Alban098/Breadboard-CPU-Emulator/schematics/ALU.kicad_sch

## KiCad design schematics/ALU.kicad_sch (2024-06-02)

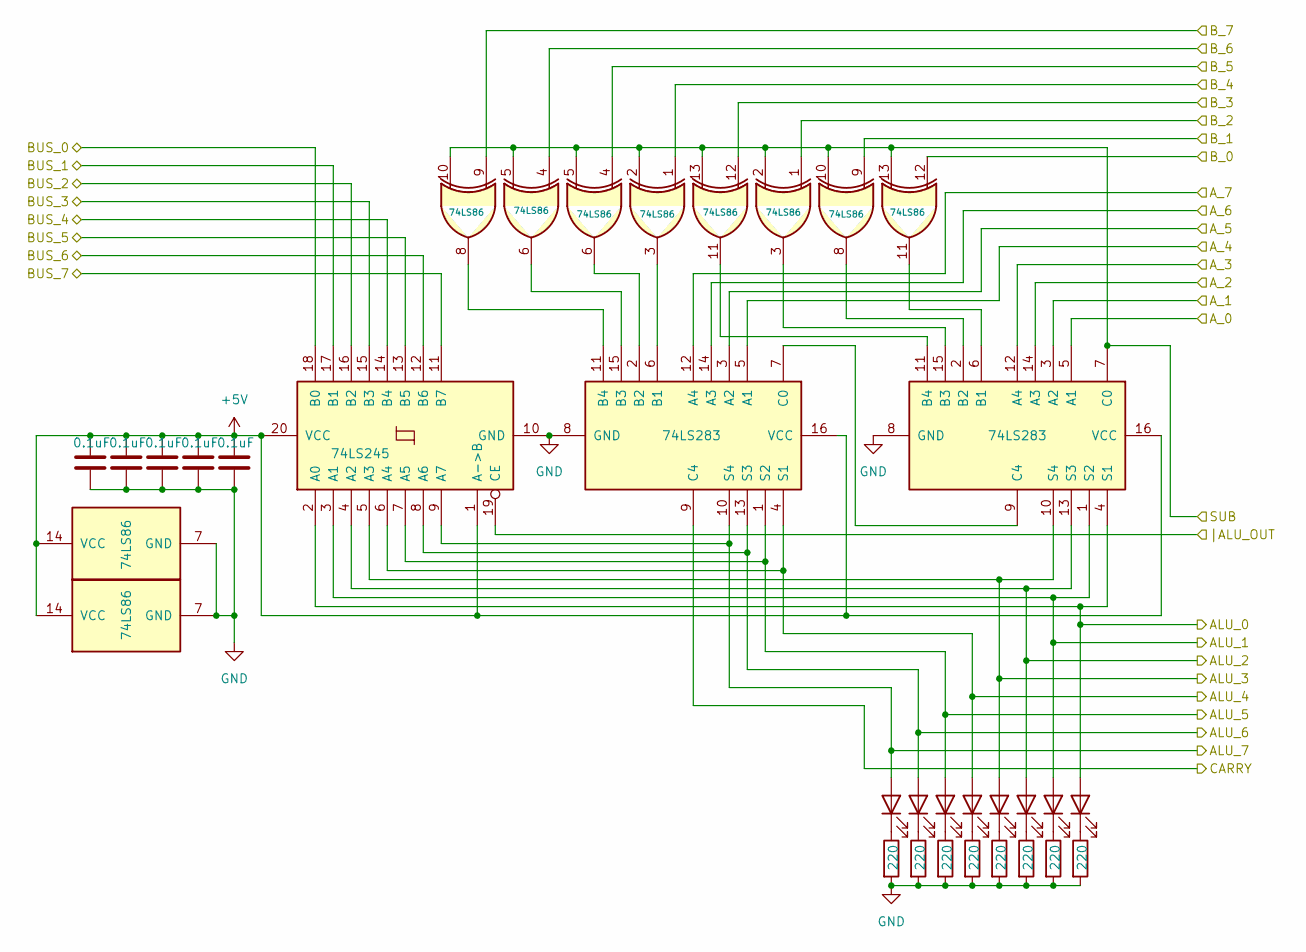
[picture p14: schematic ALU.kicad_sch]

Parts:
C1, C2, C3, C4, C5: 0.1uF
D1, D2, D3, D4, D5, D6, D7, D8: LED
R1, R2, R3, R4, R5, R6, R7, R8: 220
U1, U2: 74LS283
U3: 74LS245
U4, U5: 74LS86

Connections:
+5V: C1.1, C2.1, C3.1, C4.1, C5.1, U1.16 (VCC), U2.16 (VCC), U3.1 (A->B), U3.20 (VCC), U4.14 (VCC), U5.14 (VCC)
ALU_0: D8.2 (A), U2.4 (S1), U3.2 (A0)
ALU_1: D7.2 (A), U2.1 (S2), U3.3 (A1)
ALU_2: D6.2 (A), U2.13 (S3), U3.4 (A2)
ALU_3: D5.2 (A), U2.10 (S4), U3.5 (A3)
ALU_4: D4.2 (A), U1.4 (S1), U3.6 (A4)
ALU_5: D3.2 (A), U1.1 (S2), U3.7 (A5)
ALU_6: D2.2 (A), U1.13 (S3), U3.8 (A6)
ALU_7: D1.2 (A), U1.10 (S4), U3.9 (A7)
A_0: U2.5 (A1)
A_1: U2.3 (A2)
A_2: U2.14 (A3)
A_3: U2.12 (A4)
A_4: U1.5 (A1)
A_5: U1.3 (A2)
A_6: U1.14 (A3)
A_7: U1.12 (A4)
BUS_0: U3.18 (B0)
BUS_1: U3.17 (B1)
BUS_2: U3.16 (B2)
BUS_3: U3.15 (B3)
BUS_4: U3.14 (B4)
BUS_5: U3.13 (B5)
BUS_6: U3.12 (B6)
BUS_7: U3.11 (B7)
B_0: U5.12
B_1: U5.9
B_2: U5.1
B_3: U4.12
B_4: U4.1
B_5: U5.4
B_6: U4.4
B_7: U4.9
CARRY: U1.9 (C4)
GND: C1.2, C2.2, C3.2, C4.2, C5.2, R1.2, R2.2, R3.2, R4.2, R5.2, R6.2, R7.2, R8.2, U1.8 (GND), U2.8 (GND), U3.10 (GND), U4.7 (GND), U5.7 (GND)
unnamed: D1.1 (K), R1.1
unnamed: D2.1 (K), R2.1
unnamed: D3.1 (K), R3.1
unnamed: D4.1 (K), R4.1
unnamed: D5.1 (K), R5.1
unnamed: D6.1 (K), R6.1
unnamed: D7.1 (K), R7.1
unnamed: D8.1 (K), R8.1
unnamed: U1.2 (B2), U5.6
unnamed: U1.6 (B1), U4.3
unnamed: U1.7 (C0), U2.9 (C4)
unnamed: U1.11 (B4), U4.8
unnamed: U1.15 (B3), U4.6
unnamed: U2.2 (B2), U5.8
unnamed: U2.6 (B1), U5.11
unnamed: U2.11 (B4), U4.11
unnamed: U2.15 (B3), U5.3
SUB: U2.7 (C0), U4.2, U4.5, U4.10, U4.13, U5.2, U5.5, U5.10, U5.13
|ALU_OUT: U3.19 (CE)
