Alban098/Breadboard-CPU-Emulator/schematics/A_Register.kicad_sch

## KiCad design schematics/A_Register.kicad_sch (2024-06-02)

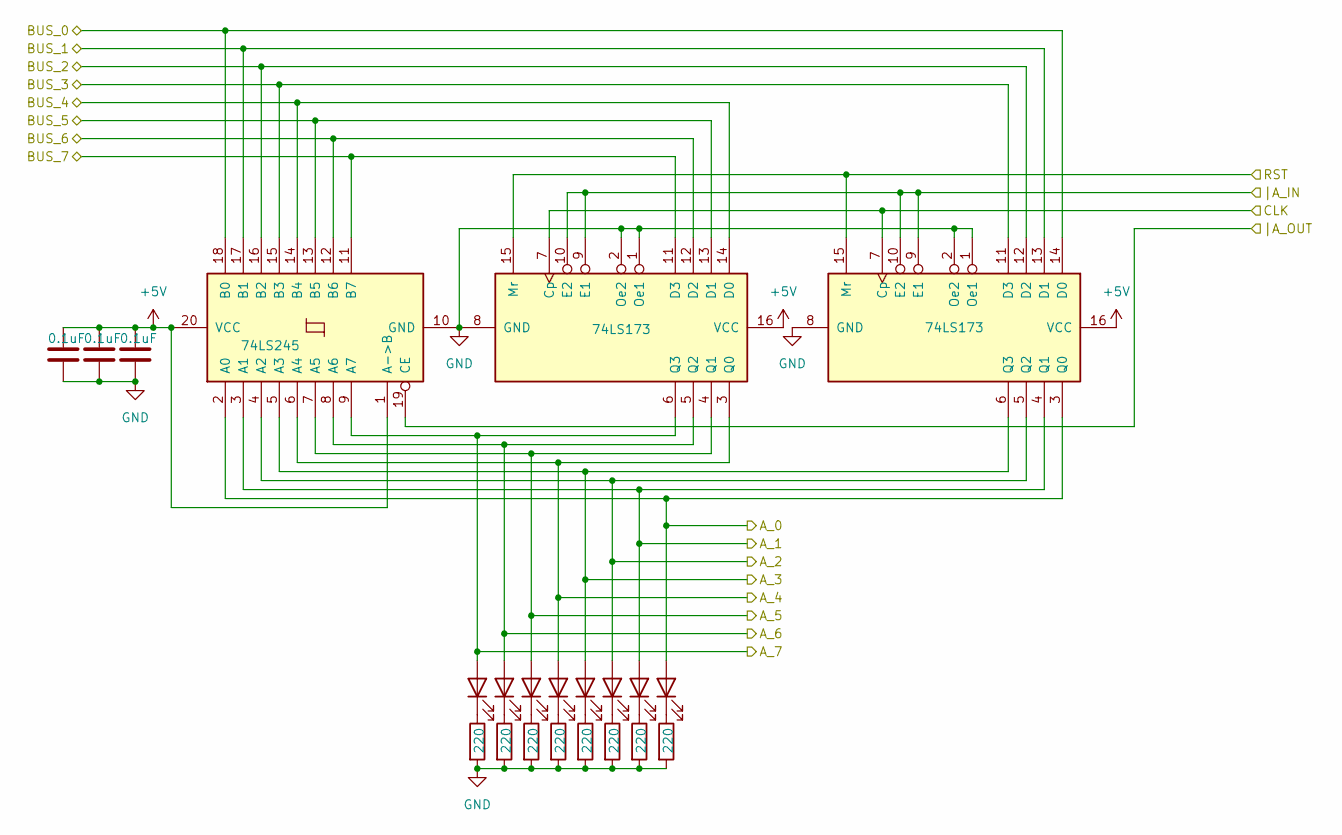
[picture p15: schematic A_Register.kicad_sch]

Parts:
C1, C2, C3: 0.1uF
D1, D2, D3, D4, D5, D6, D7, D8: LED
R1, R2, R3, R4, R5, R6, R7, R8: 220
U1, U2: 74LS173
U3: 74LS245

Connections:
+5V: C1.1, C2.1, C3.1, U1.16 (VCC), U2.16 (VCC), U3.1 (A->B), U3.20 (VCC)
A_0: D8.2 (A), U2.3 (Q0), U3.2 (A0)
A_1: D7.2 (A), U2.4 (Q1), U3.3 (A1)
A_2: D6.2 (A), U2.5 (Q2), U3.4 (A2)
A_3: D5.2 (A), U2.6 (Q3), U3.5 (A3)
A_4: D4.2 (A), U1.3 (Q0), U3.6 (A4)
A_5: D3.2 (A), U1.4 (Q1), U3.7 (A5)
A_6: D2.2 (A), U1.5 (Q2), U3.8 (A6)
A_7: D1.2 (A), U1.6 (Q3), U3.9 (A7)
BUS_0: U2.14 (D0), U3.18 (B0)
BUS_1: U2.13 (D1), U3.17 (B1)
BUS_2: U2.12 (D2), U3.16 (B2)
BUS_3: U2.11 (D3), U3.15 (B3)
BUS_4: U1.14 (D0), U3.14 (B4)
BUS_5: U1.13 (D1), U3.13 (B5)
BUS_6: U1.12 (D2), U3.12 (B6)
BUS_7: U1.11 (D3), U3.11 (B7)
CLK: U1.7 (Cp), U2.7 (Cp)
GND: C1.2, C2.2, C3.2, R1.2, R2.2, R3.2, R4.2, R5.2, R6.2, R7.2, R8.2, U1.1 (Oe1), U1.2 (Oe2), U1.8 (GND), U2.1 (Oe1), U2.2 (Oe2), U2.8 (GND), U3.10 (GND)
unnamed: D1.1 (K), R1.1
unnamed: D2.1 (K), R2.1
unnamed: D3.1 (K), R3.1
unnamed: D4.1 (K), R4.1
unnamed: D5.1 (K), R5.1
unnamed: D6.1 (K), R6.1
unnamed: D7.1 (K), R7.1
unnamed: D8.1 (K), R8.1
RST: U1.15 (Mr), U2.15 (Mr)
|A_IN: U1.9 (E1), U1.10 (E2), U2.9 (E1), U2.10 (E2)
|A_OUT: U3.19 (CE)
