Alban098/Breadboard-CPU-Emulator/schematics/Clock_Module.kicad_sch

## KiCad design schematics/Clock_Module.kicad_sch (2024-12-01)

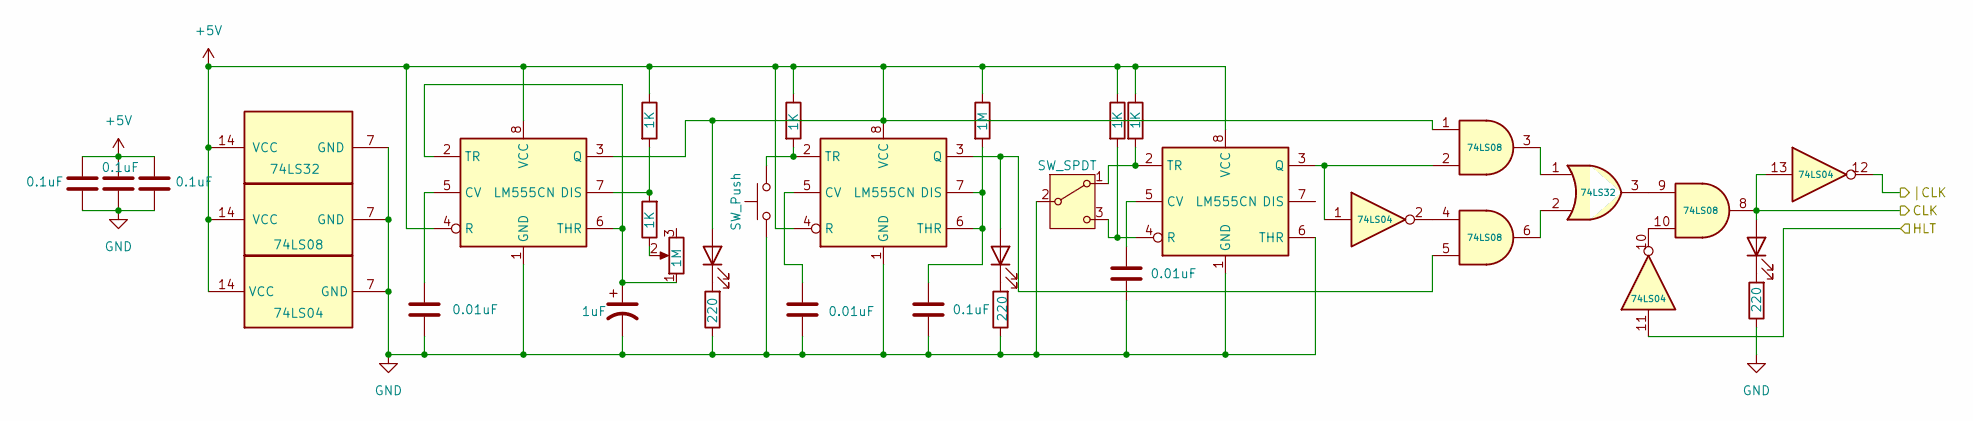
[picture p16: schematic Clock_Module.kicad_sch]

Parts:
1M: R_Potentiometer
C1, C3, C4: 0.01uF
C2, C5, C6, C8: 0.1uF
C7: 1uF
D1, D2, D3: LED
R1, R8, R9: 220
R2, R3, R4, R6, R7: 1K
R5: 1M
SW1: SW_SPDT
SW2: SW_Push
U1, U3, U7: LM555CN; DIP-8_W7.62mm
U4: 74LS08
U5: 74LS32
U6: 74LS04

Connections:
+5V: C5.2, C6.2, C8.2, D2.2 (A), R2.1, R3.1, R4.1, R5.1, R6.1, U1.3 (Q), U1.4 (R), U1.8 (VCC), U3.8 (VCC), U4.1, U4.14 (VCC), U5.14 (VCC), U6.14 (VCC), U7.4 (R), U7.8 (VCC)
CLK: D1.2 (A), U4.8, U6.13
GND: C1.2, C2.2, C3.2, C4.2, C5.1, C6.1, C7.2, C8.1, R1.1, R8.1, R9.1, SW1.2 (B), SW2.1, U1.1 (GND), U3.1 (GND), U3.6 (THR), U4.7 (GND), U5.7 (GND), U6.7 (GND), U7.1 (GND)
HLT: U6.11
unnamed: 1M.1, C7.1, U1.2 (TR), U1.6 (THR)
unnamed: 1M.2, R7.1
unnamed: C1.1, U3.5 (CV)
unnamed: C2.1, R5.2, U7.6 (THR), U7.7 (DIS)
unnamed: C3.1, U1.5 (CV)
unnamed: C4.1, U7.5 (CV)
unnamed: D1.1 (K), R1.2
unnamed: D2.1 (K), R8.2
unnamed: D3.1 (K), R9.2
unnamed: D3.2 (A), U4.5, U7.3 (Q)
unnamed: R2.2, SW1.1 (A), U3.2 (TR)
unnamed: R3.2, SW1.3 (C), U3.4 (R)
unnamed: R4.2, SW2.2, U7.2 (TR)
unnamed: R6.2, R7.2, U1.7 (DIS)
unnamed: U3.3 (Q), U4.2, U6.1
unnamed: U4.3, U5.1
unnamed: U4.4, U6.2
unnamed: U4.6, U5.2
unnamed: U4.9, U5.3
unnamed: U4.10, U6.10
|CLK: U6.12
