Alban098/Breadboard-CPU-Emulator/schematics/Control_Unit.kicad_sch

## KiCad design schematics/Control_Unit.kicad_sch (2025-01-03)

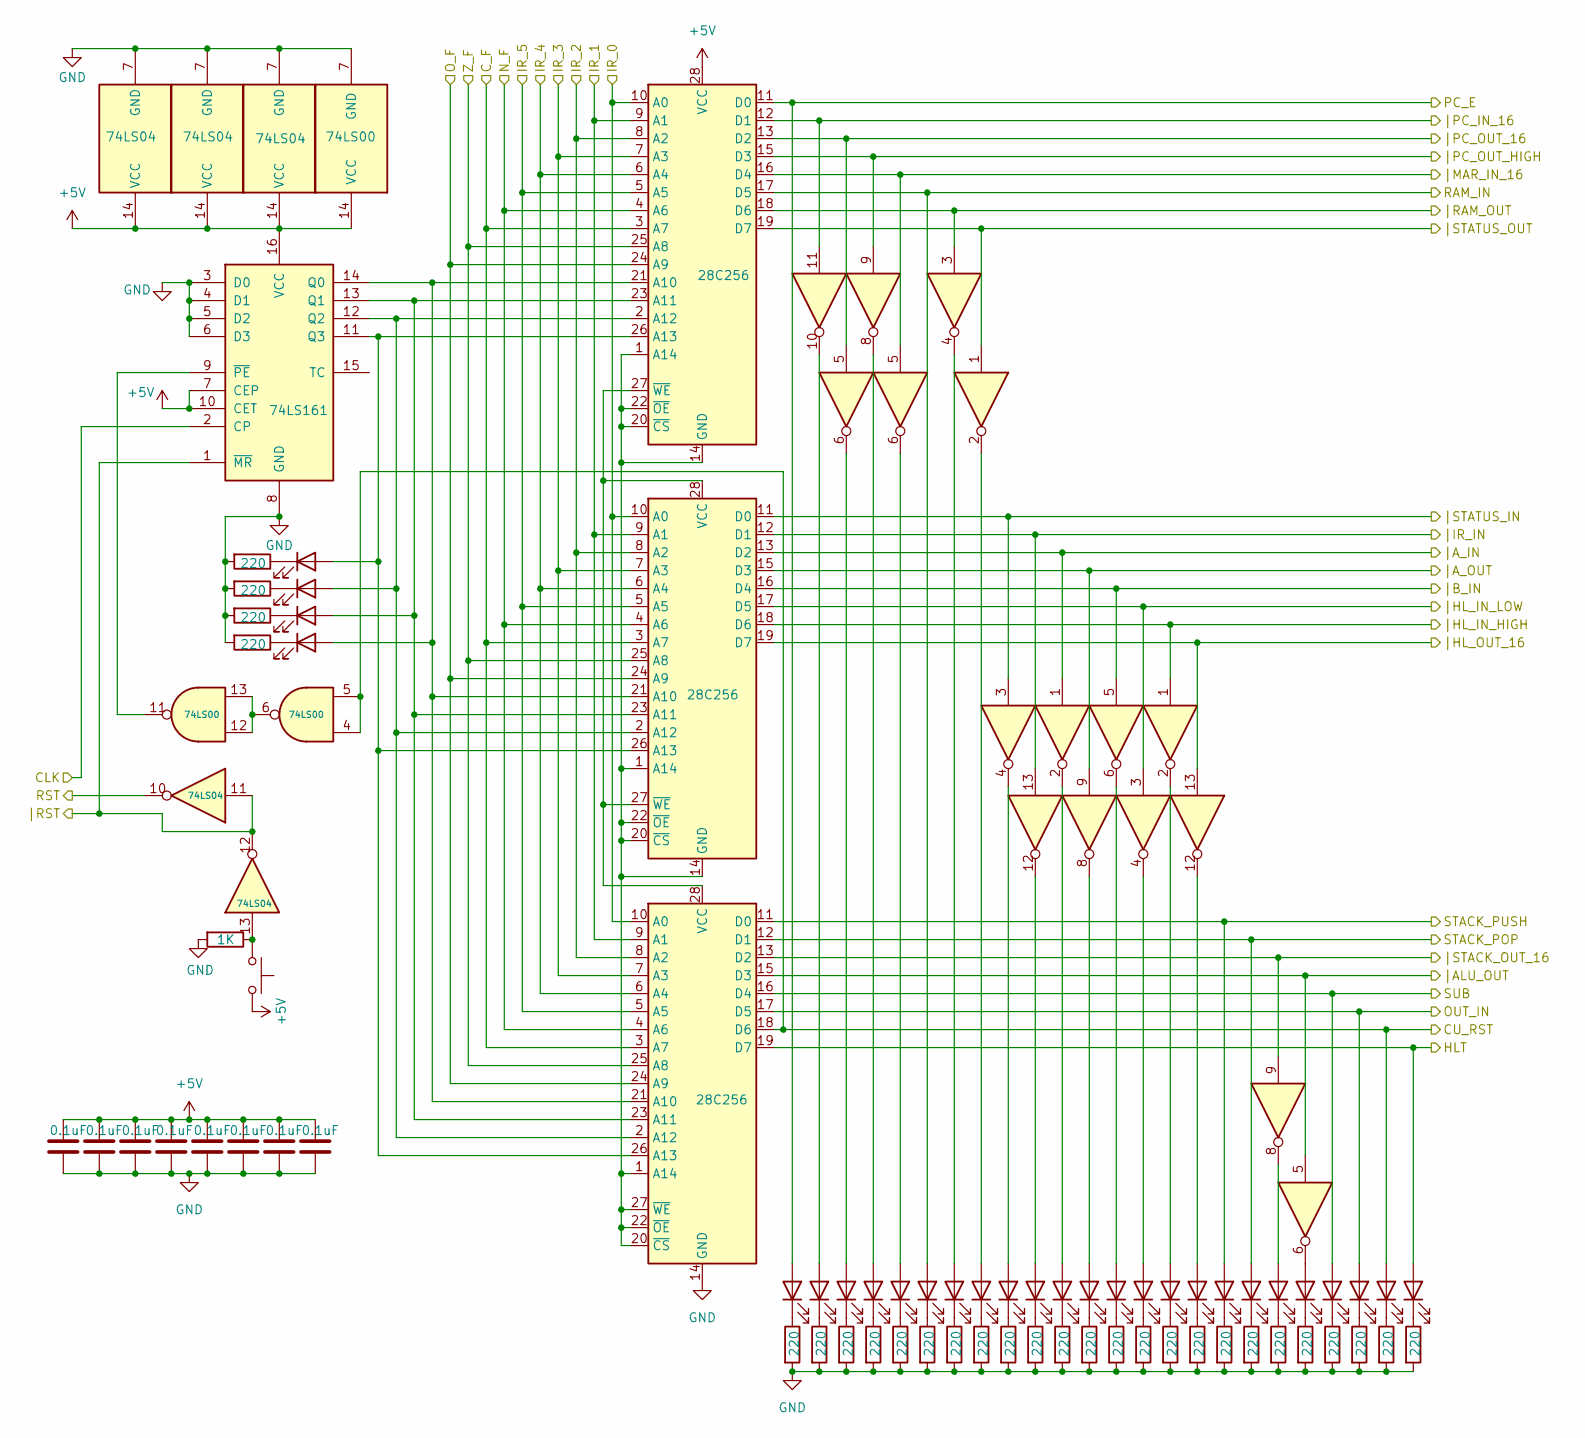
[picture p17: schematic Control_Unit.kicad_sch]

Parts:
C1, C2, C3, C4, C5, C6, C7, C8: 0.1uF
D1, D2, D3, D4, D5, D6, D7, D8, D9, D10, D11, D12, D13, D14, D15, D16, D17, D18, D19, D20, D21, D22, D23, D24, D25, D28, D29, D30: LED
R1, R2, R3, R4, R5, R6, R7, R8, R9, R10, R11, R12, R13, R14, R15, R16, R18, R19, R20, R21, R22, R23, R24, R25, R26, R29, R30, R31: 220
R17: 1K
SW1: SW_Push
U1, U2, U4: 28C256
U3: 74LS161
U5: 74LS00
U6, U7, U8, U9: 74LS04

Connections:
+5V: C1.1, C2.1, C3.1, C4.1, C5.1, C6.1, C7.1, C8.1, SW1.2, U1.28 (VCC), U3.7 (CEP), U3.10 (CET), U3.16 (VCC), U5.14 (VCC), U6.14 (VCC), U7.14 (VCC), U8.14 (VCC)
CLK: U3.2 (CP)
CU_RST: D24.2 (A), U4.18 (D6), U5.4, U5.5
C_F: U1.3 (A7), U2.3 (A7), U4.3 (A7)
GND: C1.2, C2.2, C3.2, C4.2, C5.2, C6.2, C7.2, C8.2, R1.2, R2.2, R3.2, R4.2, R5.2, R6.2, R7.2, R8.2, R9.2, R10.2, R11.2, R12.2, R13.2, R14.2, R15.2, R16.2, R17.2, R18.2, R19.2, R20.2, R21.2, R22.2, R23.2, R24.2, R25.2, R26.2, R29.2, R30.2, R31.2, U3.3 (D0), U3.4 (D1), U3.5 (D2), U3.6 (D3), U3.8 (GND), U4.14 (GND), U5.7 (GND), U6.7 (GND), U7.7 (GND), U8.7 (GND)
HLT: D25.2 (A), U4.19 (D7)
IR_0: U1.10 (A0), U2.10 (A0), U4.10 (A0)
IR_1: U1.9 (A1), U2.9 (A1), U4.9 (A1)
IR_2: U1.8 (A2), U2.8 (A2), U4.8 (A2)
IR_3: U1.7 (A3), U2.7 (A3), U4.7 (A3)
IR_4: U1.6 (A4), U2.6 (A4), U4.6 (A4)
IR_5: U1.5 (A5), U2.5 (A5), U4.5 (A5)
N_F: U1.4 (A6), U2.4 (A6), U4.4 (A6)
unnamed: D1.1 (K), R1.1
unnamed: D2.1 (K), R2.1
unnamed: D2.2 (A), U6.10
unnamed: D3.1 (K), R3.1
unnamed: D3.2 (A), U9.6
unnamed: D4.1 (K), R4.1
unnamed: D4.2 (A), U6.8
unnamed: D5.1 (K), R5.1
unnamed: D5.2 (A), U6.6
unnamed: D6.1 (K), R6.1
unnamed: D7.1 (K), R7.1
unnamed: D7.2 (A), U6.4
unnamed: D8.1 (K), R8.1
unnamed: D8.2 (A), U6.2
unnamed: D9.1 (K), R9.1
unnamed: D9.2 (A), U8.4
unnamed: D10.1 (K), R10.1
unnamed: D10.2 (A), U8.12
unnamed: D11.1 (K), R11.1
unnamed: D11.2 (A), U8.2
unnamed: D12.1 (K), R12.1
unnamed: D12.2 (A), U7.8
unnamed: D13.1 (K), R13.1
unnamed: D13.2 (A), U7.6
unnamed: D14.1 (K), R14.1
unnamed: D14.2 (A), U7.4
unnamed: D15.1 (K), R15.1
unnamed: D15.2 (A), U7.2
unnamed: D16.1 (K), R16.1
unnamed: D16.2 (A), U6.12
unnamed: D17.1 (K), R18.1
unnamed: D17.2 (A), U1.21 (A10), U2.21 (A10), U3.14 (Q0), U4.21 (A10)
unnamed: D18.1 (K), R19.1
unnamed: D19.1 (K), R20.1
unnamed: D20.1 (K), R21.1
unnamed: D20.2 (A), U8.8
unnamed: D21.1 (K), R22.1
unnamed: D21.2 (A), U8.6
unnamed: D22.1 (K), R23.1
unnamed: D23.1 (K), R24.1
unnamed: D24.1 (K), R25.1
unnamed: D25.1 (K), R26.1
unnamed: D28.1 (K), R29.1
unnamed: D28.2 (A), U1.23 (A11), U2.23 (A11), U3.13 (Q1), U4.23 (A11)
unnamed: D29.1 (K), R30.1
unnamed: D29.2 (A), U1.26 (A13), U2.26 (A13), U3.11 (Q3), U4.26 (A13)
unnamed: D30.1 (K), R31.1
unnamed: D30.2 (A), U1.2 (A12), U2.2 (A12), U3.12 (Q2), U4.2 (A12)
unnamed: R17.1, SW1.1, U7.13
unnamed: U1.1 (A14), U1.14 (GND), U1.20 (~CS), U1.22 (~OE), U2.1 (A14), U2.14 (GND), U2.20 (~CS), U2.22 (~OE), U4.1 (A14), U4.20 (~CS), U4.22 (~OE), U4.27 (~WE)
unnamed: U1.27 (~WE), U2.27 (~WE), U2.28 (VCC), U4.28 (VCC)
unnamed: U3.9 (~PE), U5.11
unnamed: U5.6, U5.12, U5.13
OUT_IN: D23.2 (A), U4.17 (D5)
O_F: U1.24 (A9), U2.24 (A9), U4.24 (A9)
PC_E: D1.2 (A), U1.11 (D0)
RAM_IN: D6.2 (A), U1.17 (D5)
RST: U7.10
STACK_POP: D19.2 (A), U4.12 (D1)
STACK_PUSH: D18.2 (A), U4.11 (D0)
SUB: D22.2 (A), U4.16 (D4)
Z_F: U1.25 (A8), U2.25 (A8), U4.25 (A8)
|ALU_OUT: U4.15 (D3), U8.5
|A_IN: U2.13 (D2), U8.1
|A_OUT: U2.15 (D3), U7.9
|B_IN: U2.16 (D4), U7.5
|HL_IN_HIGH: U2.18 (D6), U7.1
|HL_IN_LOW: U2.17 (D5), U7.3
|HL_OUT_16: U2.19 (D7), U6.13
|IR_IN: U2.12 (D1), U8.13
|MAR_IN_16: U1.16 (D4), U6.5
|PC_IN_16: U1.12 (D1), U6.11
|PC_OUT_16: U1.13 (D2), U9.5
|PC_OUT_HIGH: U1.15 (D3), U6.9
|RAM_OUT: U1.18 (D6), U6.3
|RST: U3.1 (~MR), U7.11, U7.12
|STACK_OUT_16: U4.13 (D2), U8.9
|STATUS_IN: U2.11 (D0), U8.3
|STATUS_OUT: U1.19 (D7), U6.1
