Alban098/Breadboard-CPU-Emulator/schematics/HL_Register.kicad_sch

## KiCad design schematics/HL_Register.kicad_sch (2024-06-02)

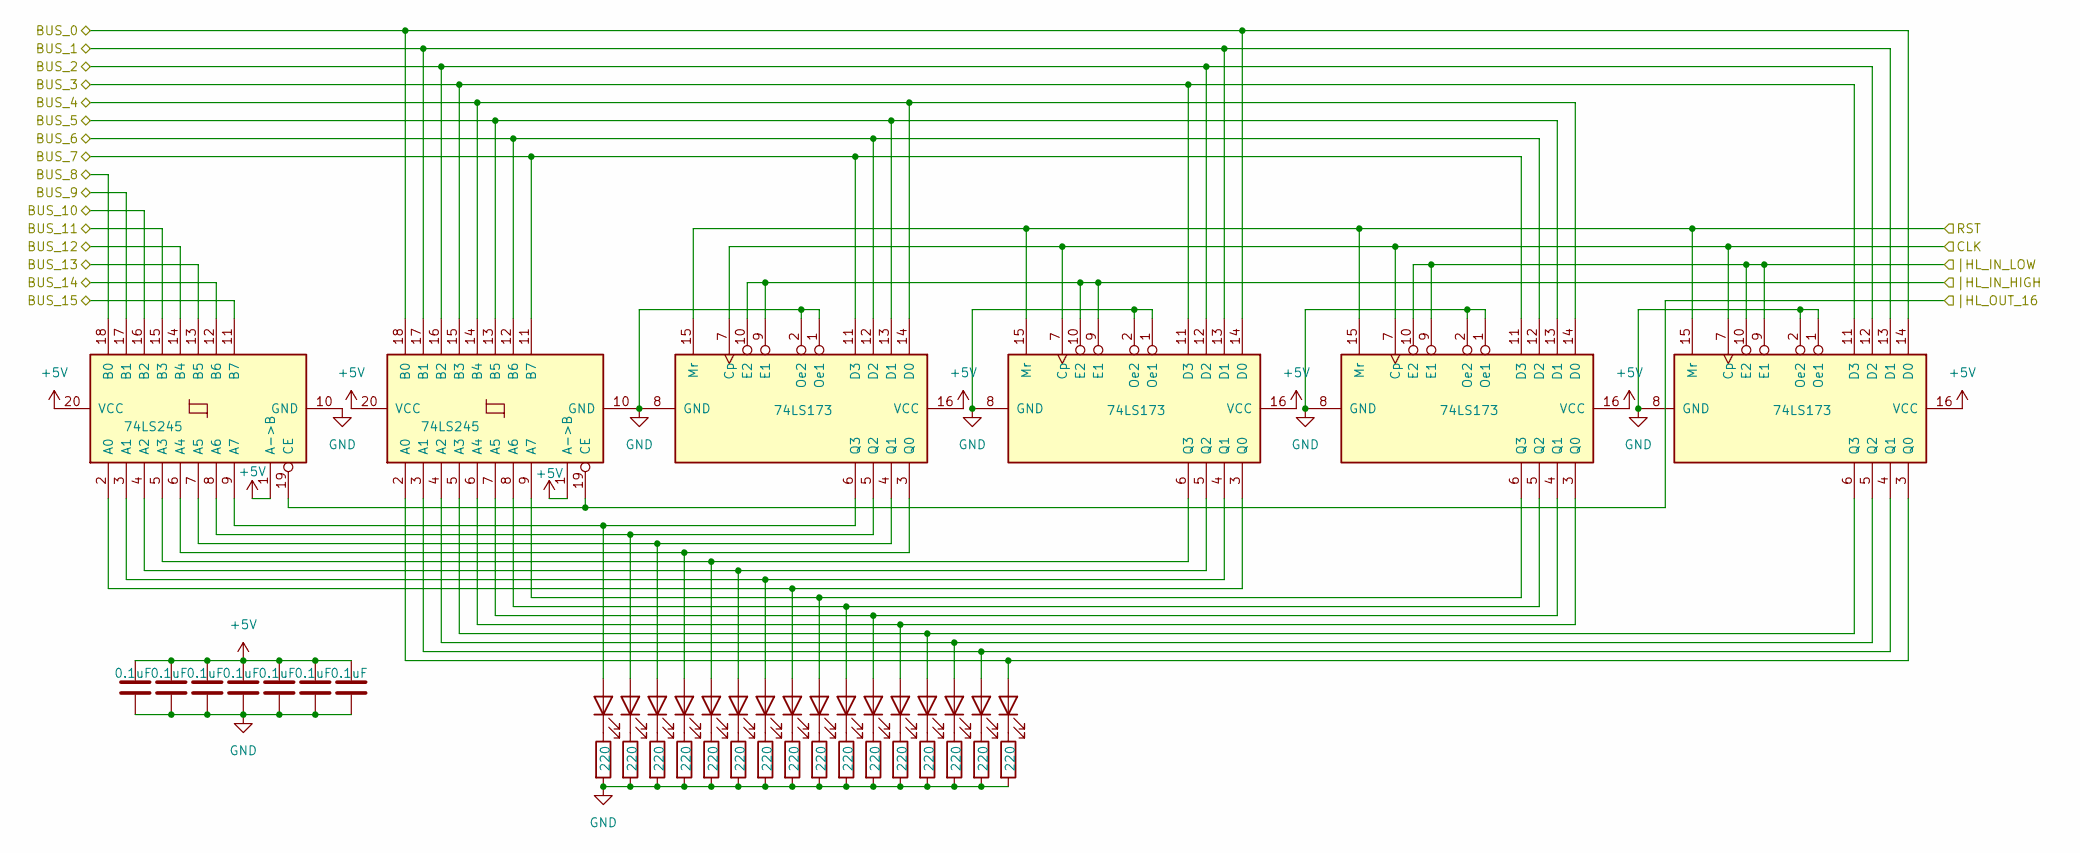
[picture p18: schematic HL_Register.kicad_sch]

Parts:
C1, C2, C3, C4, C5, C6, C7: 0.1uF
D1, D2, D3, D4, D5, D6, D7, D8, D9, D10, D11, D12, D13, D14, D15, D16: LED
R1, R2, R3, R4, R5, R6, R7, R8, R9, R10, R11, R12, R13, R14, R15, R16: 220
U1, U2, U4, U8: 74LS173
U6, U7: 74LS245

Connections:
+5V: C1.1, C2.1, C3.1, C4.1, C5.1, C6.1, C7.1, U1.16 (VCC), U2.16 (VCC), U4.16 (VCC), U6.1 (A->B), U6.20 (VCC), U7.1 (A->B), U7.20 (VCC), U8.16 (VCC)
BUS_0: U1.14 (D0), U4.14 (D0), U6.18 (B0)
BUS_1: U1.13 (D1), U4.13 (D1), U6.17 (B1)
BUS_2: U1.12 (D2), U4.12 (D2), U6.16 (B2)
BUS_3: U1.11 (D3), U4.11 (D3), U6.15 (B3)
BUS_4: U2.14 (D0), U6.14 (B4), U8.14 (D0)
BUS_5: U2.13 (D1), U6.13 (B5), U8.13 (D1)
BUS_6: U2.12 (D2), U6.12 (B6), U8.12 (D2)
BUS_7: U2.11 (D3), U6.11 (B7), U8.11 (D3)
BUS_8: U7.18 (B0)
BUS_9: U7.17 (B1)
BUS_10: U7.16 (B2)
BUS_11: U7.15 (B3)
BUS_12: U7.14 (B4)
BUS_13: U7.13 (B5)
BUS_14: U7.12 (B6)
BUS_15: U7.11 (B7)
CLK: U1.7 (Cp), U2.7 (Cp), U4.7 (Cp), U8.7 (Cp)
GND: C1.2, C2.2, C3.2, C4.2, C5.2, C6.2, C7.2, R1.2, R2.2, R3.2, R4.2, R5.2, R6.2, R7.2, R8.2, R9.2, R10.2, R11.2, R12.2, R13.2, R14.2, R15.2, R16.2, U1.1 (Oe1), U1.2 (Oe2), U1.8 (GND), U2.1 (Oe1), U2.2 (Oe2), U2.8 (GND), U4.1 (Oe1), U4.2 (Oe2), U4.8 (GND), U6.10 (GND), U7.10 (GND), U8.1 (Oe1), U8.2 (Oe2), U8.8 (GND)
unnamed: D1.1 (K), R1.1
unnamed: D1.2 (A), U7.9 (A7), U8.6 (Q3)
unnamed: D2.1 (K), R2.1
unnamed: D2.2 (A), U7.8 (A6), U8.5 (Q2)
unnamed: D3.1 (K), R3.1
unnamed: D3.2 (A), U7.7 (A5), U8.4 (Q1)
unnamed: D4.1 (K), R4.1
unnamed: D4.2 (A), U7.6 (A4), U8.3 (Q0)
unnamed: D5.1 (K), R5.1
unnamed: D5.2 (A), U1.6 (Q3), U7.5 (A3)
unnamed: D6.1 (K), R6.1
unnamed: D6.2 (A), U1.5 (Q2), U7.4 (A2)
unnamed: D7.1 (K), R7.1
unnamed: D7.2 (A), U1.4 (Q1), U7.3 (A1)
unnamed: D8.1 (K), R8.1
unnamed: D8.2 (A), U1.3 (Q0), U7.2 (A0)
unnamed: D9.1 (K), R9.1
unnamed: D9.2 (A), U2.6 (Q3), U6.9 (A7)
unnamed: D10.1 (K), R10.1
unnamed: D10.2 (A), U2.5 (Q2), U6.8 (A6)
unnamed: D11.1 (K), R11.1
unnamed: D11.2 (A), U2.4 (Q1), U6.7 (A5)
unnamed: D12.1 (K), R12.1
unnamed: D12.2 (A), U2.3 (Q0), U6.6 (A4)
unnamed: D13.1 (K), R13.1
unnamed: D13.2 (A), U4.6 (Q3), U6.5 (A3)
unnamed: D14.1 (K), R14.1
unnamed: D14.2 (A), U4.5 (Q2), U6.4 (A2)
unnamed: D15.1 (K), R15.1
unnamed: D15.2 (A), U4.4 (Q1), U6.3 (A1)
unnamed: D16.1 (K), R16.1
unnamed: D16.2 (A), U4.3 (Q0), U6.2 (A0)
RST: U1.15 (Mr), U2.15 (Mr), U4.15 (Mr), U8.15 (Mr)
|HL_IN_HIGH: U1.9 (E1), U1.10 (E2), U8.9 (E1), U8.10 (E2)
|HL_IN_LOW: U2.9 (E1), U2.10 (E2), U4.9 (E1), U4.10 (E2)
|HL_OUT_16: U6.19 (CE), U7.19 (CE)
