Alban098/Breadboard-CPU-Emulator/schematics/Memory.kicad_sch

## KiCad design schematics/Memory.kicad_sch (2024-12-01)

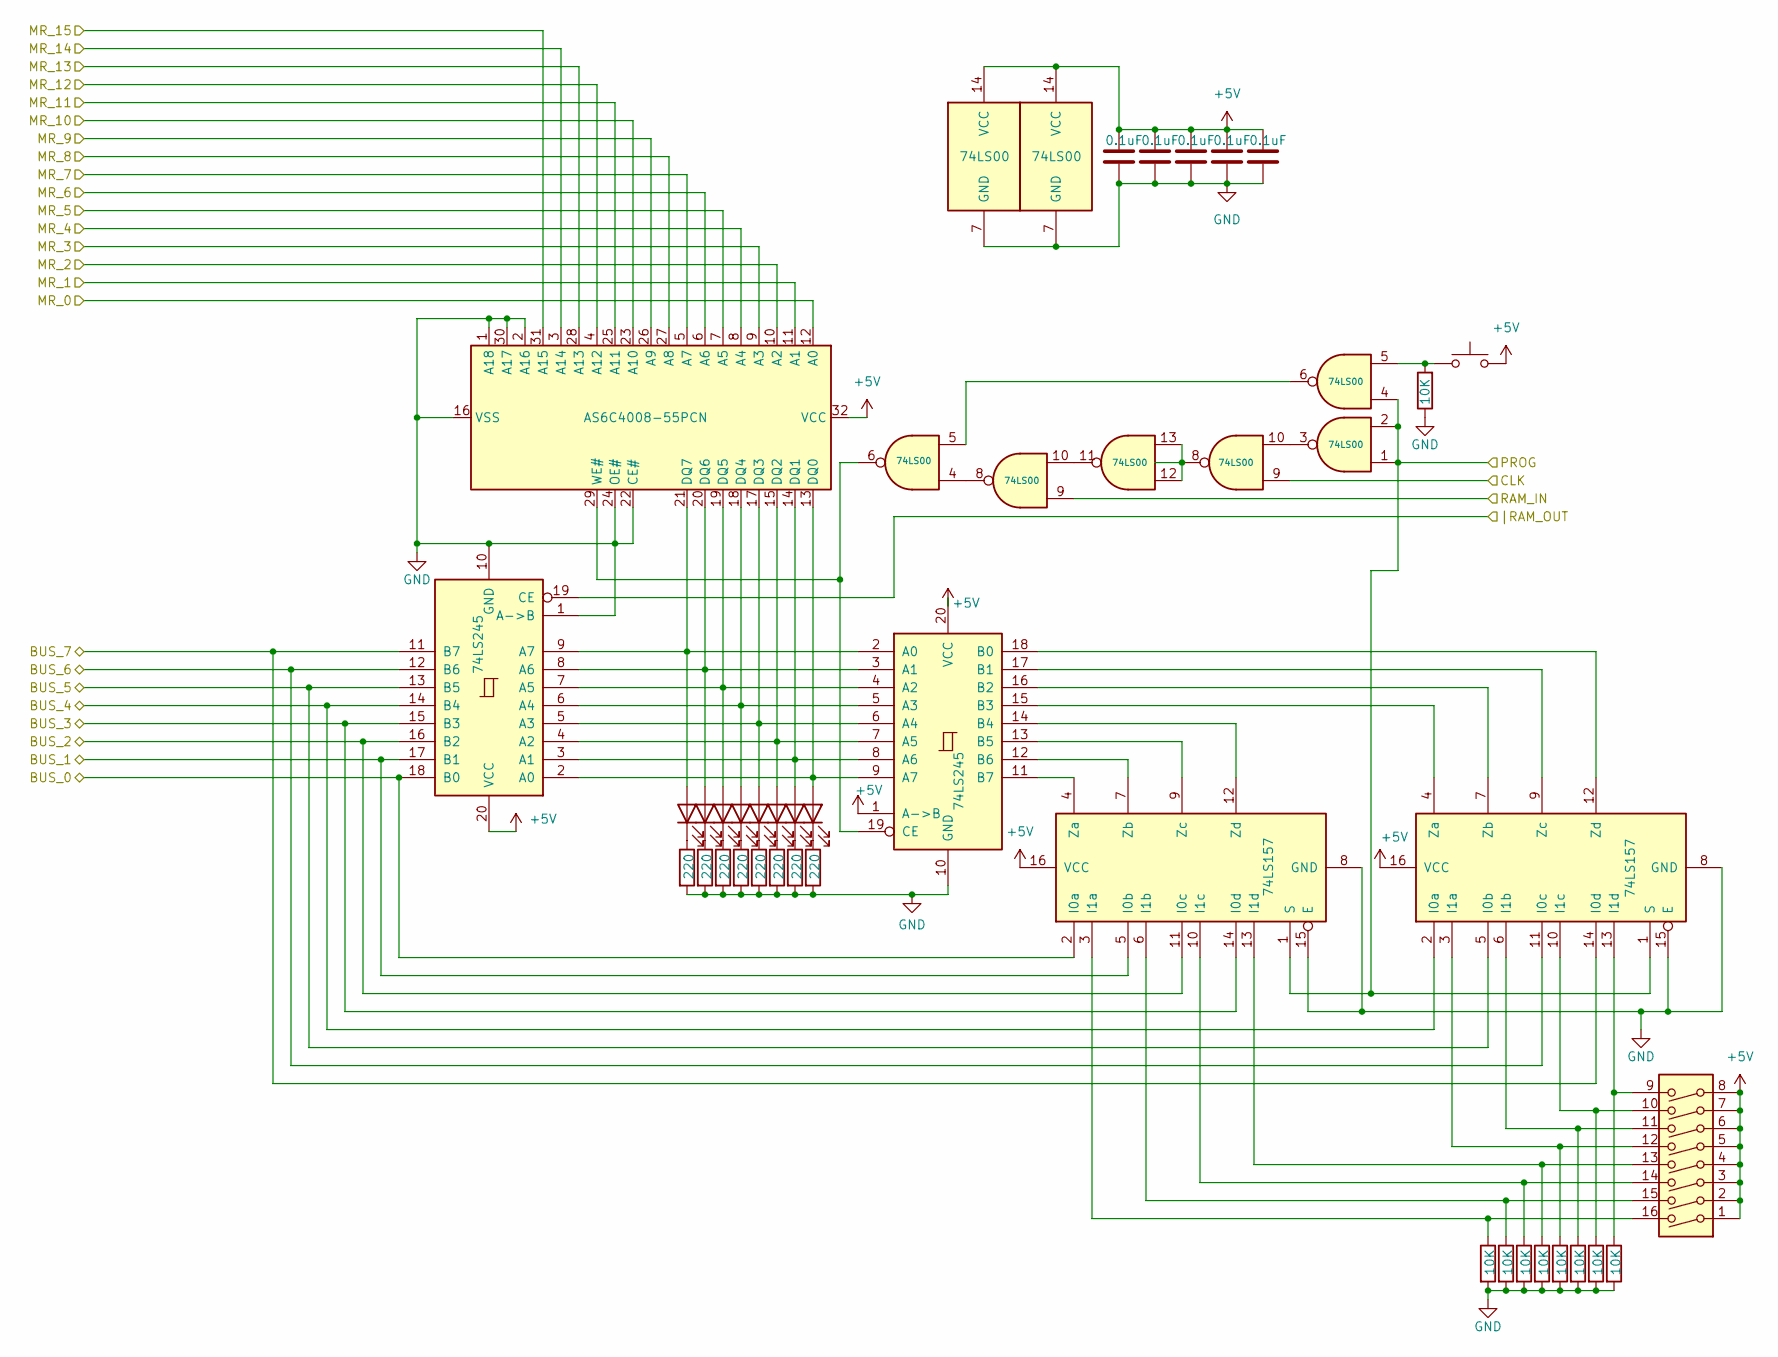
[picture p19: schematic Memory.kicad_sch]

Parts:
C1, C3, C4, C7, C8: 0.1uF
D1, D2, D3, D4, D5, D6, D7, D8: LED
R1, R2, R3, R4, R5, R6, R7, R8: 220
R9, R10, R11, R12, R13, R14, R15, R16, R17: 10K
SW1: SW_DIP_x08
SW2: SW_Push
U1: AS6C4008-55PCN; DIP-32_W15.24mm
U2, U5: 74LS245
U3, U6: 74LS157
U4, U7: 74LS00

Connections:
+5V: C1.1, C3.1, C4.1, C7.1, C8.1, SW1.1, SW1.2, SW1.3, SW1.4, SW1.5, SW1.6, SW1.7, SW1.8, SW2.2, U1.32 (VCC), U2.20 (VCC), U3.16 (VCC), U4.14 (VCC), U5.1 (A->B), U5.20 (VCC), U6.16 (VCC), U7.14 (VCC)
BUS_0: U2.18 (B0), U3.2 (I0a)
BUS_1: U2.17 (B1), U3.5 (I0b)
BUS_2: U2.16 (B2), U3.11 (I0c)
BUS_3: U2.15 (B3), U3.14 (I0d)
BUS_4: U2.14 (B4), U6.2 (I0a)
BUS_5: U2.13 (B5), U6.5 (I0b)
BUS_6: U2.12 (B6), U6.11 (I0c)
BUS_7: U2.11 (B7), U6.14 (I0d)
CLK: U7.9
GND: C1.2, C3.2, C4.2, C7.2, C8.2, R1.2, R2.2, R3.2, R4.2, R5.2, R6.2, R7.2, R8.2, R9.1, R10.2, R11.2, R12.2, R13.2, R14.2, R15.2, R16.2, R17.2, U1.1 (A18), U1.2 (A16), U1.16 (VSS), U1.22 (CE#), U1.24 (OE#), U1.30 (A17), U2.1 (A->B), U2.10 (GND), U3.8 (GND), U3.15 (E), U4.7 (GND), U5.10 (GND), U6.8 (GND), U6.15 (E), U7.7 (GND)
MR_0: U1.12 (A0)
MR_1: U1.11 (A1)
MR_2: U1.10 (A2)
MR_3: U1.9 (A3)
MR_4: U1.8 (A4)
MR_5: U1.7 (A5)
MR_6: U1.6 (A6)
MR_7: U1.5 (A7)
MR_8: U1.27 (A8)
MR_9: U1.26 (A9)
MR_10: U1.23 (A10)
MR_11: U1.25 (A11)
MR_12: U1.4 (A12)
MR_13: U1.28 (A13)
MR_14: U1.3 (A14)
MR_15: U1.31 (A15)
unnamed: D1.1 (K), R1.1
unnamed: D1.2 (A), U1.21 (DQ7), U2.9 (A7), U5.2 (A0)
unnamed: D2.1 (K), R2.1
unnamed: D2.2 (A), U1.20 (DQ6), U2.8 (A6), U5.3 (A1)
unnamed: D3.1 (K), R3.1
unnamed: D3.2 (A), U1.19 (DQ5), U2.7 (A5), U5.4 (A2)
unnamed: D4.1 (K), R4.1
unnamed: D4.2 (A), U1.18 (DQ4), U2.6 (A4), U5.5 (A3)
unnamed: D5.1 (K), R5.1
unnamed: D5.2 (A), U1.17 (DQ3), U2.5 (A3), U5.6 (A4)
unnamed: D6.1 (K), R6.1
unnamed: D6.2 (A), U1.15 (DQ2), U2.4 (A2), U5.7 (A5)
unnamed: D7.1 (K), R7.1
unnamed: D7.2 (A), U1.14 (DQ1), U2.3 (A1), U5.8 (A6)
unnamed: D8.1 (K), R8.1
unnamed: D8.2 (A), U1.13 (DQ0), U2.2 (A0), U5.9 (A7)
unnamed: R9.2, SW2.1, U4.5
unnamed: R10.1, SW1.9, U6.13 (I1d)
unnamed: R11.1, SW1.10, U6.10 (I1c)
unnamed: R12.1, SW1.11, U6.6 (I1b)
unnamed: R13.1, SW1.12, U6.3 (I1a)
unnamed: R14.1, SW1.13, U3.13 (I1d)
unnamed: R15.1, SW1.14, U3.10 (I1c)
unnamed: R16.1, SW1.15, U3.6 (I1b)
unnamed: R17.1, SW1.16, U3.3 (I1a)
unnamed: U1.29 (WE#), U5.19 (CE), U7.6
unnamed: U3.4 (Za), U5.11 (B7)
unnamed: U3.7 (Zb), U5.12 (B6)
unnamed: U3.9 (Zc), U5.13 (B5)
unnamed: U3.12 (Zd), U5.14 (B4)
unnamed: U4.3, U7.10
unnamed: U4.6, U7.5
unnamed: U4.8, U7.4
unnamed: U4.10, U4.11
unnamed: U4.12, U4.13, U7.8
unnamed: U5.15 (B3), U6.4 (Za)
unnamed: U5.16 (B2), U6.7 (Zb)
unnamed: U5.17 (B1), U6.9 (Zc)
unnamed: U5.18 (B0), U6.12 (Zd)
PROG: U3.1 (S), U4.1, U4.2, U4.4, U6.1 (S)
RAM_IN: U4.9
|RAM_OUT: U2.19 (CE)
