Alban098/Breadboard-CPU-Emulator/schematics/Memory_Address_Register.kicad_sch

## KiCad design schematics/Memory_Address_Register.kicad_sch (2024-12-01)

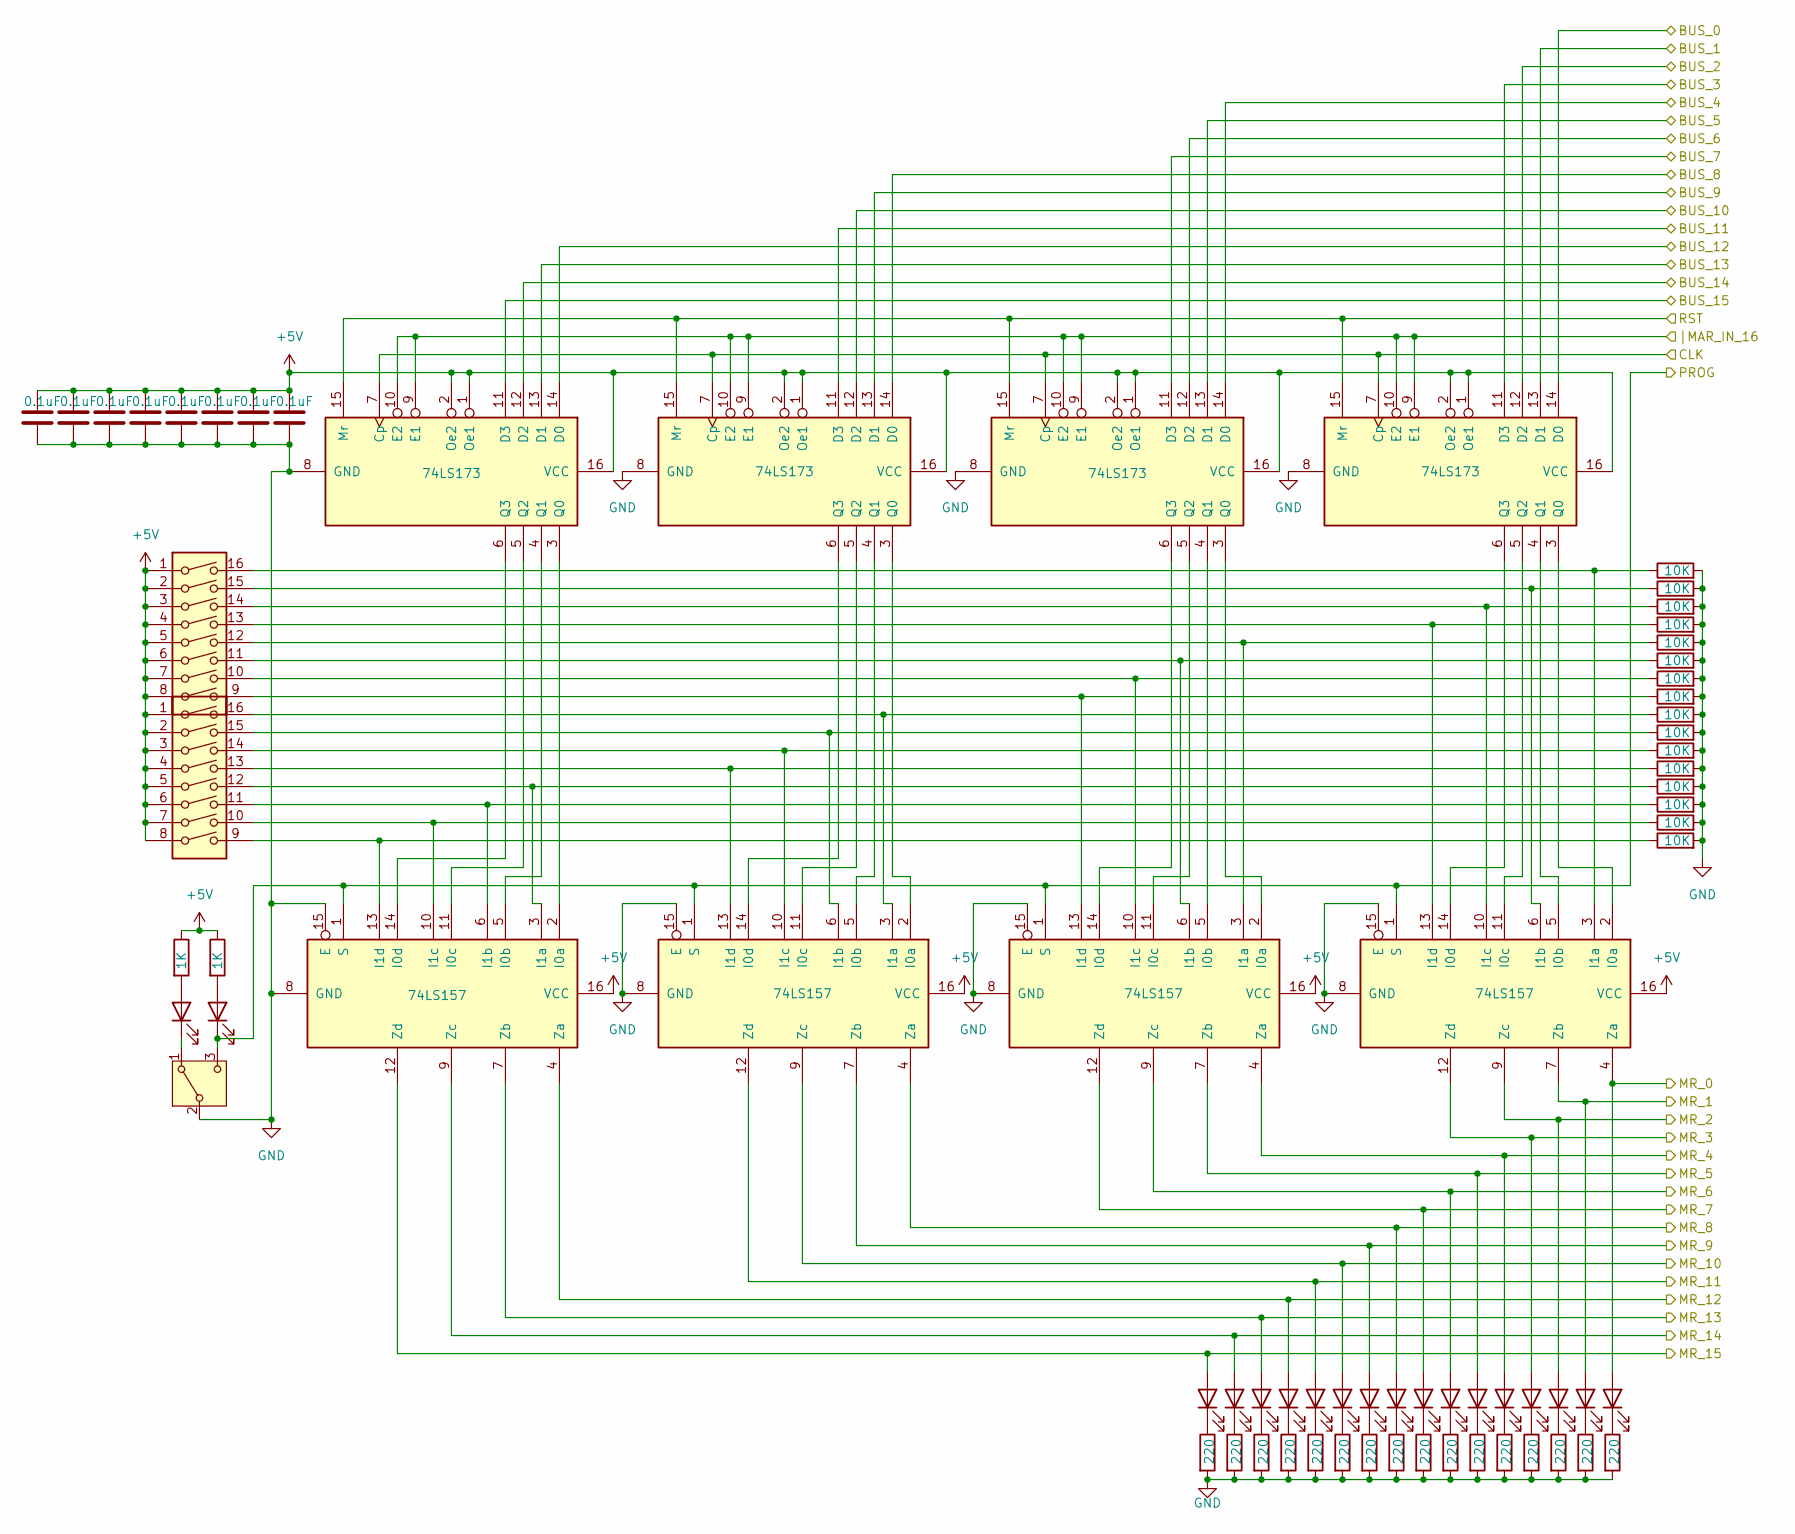
[picture p20: schematic Memory_Address_Register.kicad_sch]

Parts:
C1, C2, C3, C4, C5, C6, C7, C8: 0.1uF
D1, D2, D3, D4, D5, D6, D7, D8, D9, D10, D11, D12, D13, D14, D15, D16, D17, D18: LED
R1, R2, R3, R4, R5, R6, R7, R8, R11, R12, R13, R14, R15, R16, R17, R18: 220
R9, R10: 1K
R19, R20, R21, R22, R23, R24, R25, R26, R27, R28, R29, R30, R31, R32, R33, R34: 10K
SW1, SW3: SW_DIP_x08
SW2: SW_SPDT
U1, U2, U5, U6: 74LS173
U3, U4, U7, U8: 74LS157

Connections:
+5V: C1.1, C2.1, C3.1, C4.1, C5.1, C6.1, C7.1, C8.1, R9.1, R10.1, SW1.1, SW1.2, SW1.3, SW1.4, SW1.5, SW1.6, SW1.7, SW1.8, SW3.1, SW3.2, SW3.3, SW3.4, SW3.5, SW3.6, SW3.7, SW3.8, U1.1 (Oe1), U1.2 (Oe2), U1.16 (VCC), U2.1 (Oe1), U2.2 (Oe2), U2.16 (VCC), U3.16 (VCC), U4.16 (VCC), U5.1 (Oe1), U5.2 (Oe2), U5.16 (VCC), U6.1 (Oe1), U6.2 (Oe2), U6.16 (VCC), U7.16 (VCC), U8.16 (VCC)
BUS_0: U6.14 (D0)
BUS_1: U6.13 (D1)
BUS_2: U6.12 (D2)
BUS_3: U6.11 (D3)
BUS_4: U5.14 (D0)
BUS_5: U5.13 (D1)
BUS_6: U5.12 (D2)
BUS_7: U5.11 (D3)
BUS_8: U2.14 (D0)
BUS_9: U2.13 (D1)
BUS_10: U2.12 (D2)
BUS_11: U2.11 (D3)
BUS_12: U1.14 (D0)
BUS_13: U1.13 (D1)
BUS_14: U1.12 (D2)
BUS_15: U1.11 (D3)
CLK: U1.7 (Cp), U2.7 (Cp), U5.7 (Cp), U6.7 (Cp)
GND: C1.2, C2.2, C3.2, C4.2, C5.2, C6.2, C7.2, C8.2, R1.2, R2.2, R3.2, R4.2, R5.2, R6.2, R7.2, R8.2, R11.2, R12.2, R13.2, R14.2, R15.2, R16.2, R17.2, R18.2, R19.2, R20.2, R21.2, R22.2, R23.2, R24.2, R25.2, R26.2, R27.2, R28.2, R29.2, R30.2, R31.2, R32.2, R33.2, R34.2, SW2.2 (B), U1.8 (GND), U2.8 (GND), U3.8 (GND), U3.15 (E), U4.8 (GND), U4.15 (E), U5.8 (GND), U6.8 (GND), U7.8 (GND), U7.15 (E), U8.8 (GND), U8.15 (E)
MR_0: D18.2 (A), U8.4 (Za)
MR_1: D17.2 (A), U8.7 (Zb)
MR_2: D16.2 (A), U8.9 (Zc)
MR_3: D15.2 (A), U8.12 (Zd)
MR_4: D14.2 (A), U7.4 (Za)
MR_5: D13.2 (A), U7.7 (Zb)
MR_6: D12.2 (A), U7.9 (Zc)
MR_7: D11.2 (A), U7.12 (Zd)
MR_8: D8.2 (A), U3.4 (Za)
MR_9: D7.2 (A), U3.7 (Zb)
MR_10: D6.2 (A), U3.9 (Zc)
MR_11: D5.2 (A), U3.12 (Zd)
MR_12: D4.2 (A), U4.4 (Za)
MR_13: D3.2 (A), U4.7 (Zb)
MR_14: D2.2 (A), U4.9 (Zc)
MR_15: D1.2 (A), U4.12 (Zd)
unnamed: D1.1 (K), R1.1
unnamed: D2.1 (K), R2.1
unnamed: D3.1 (K), R3.1
unnamed: D4.1 (K), R4.1
unnamed: D5.1 (K), R5.1
unnamed: D6.1 (K), R6.1
unnamed: D7.1 (K), R7.1
unnamed: D8.1 (K), R8.1
unnamed: D9.1 (K), SW2.1 (A)
unnamed: D9.2 (A), R9.2
unnamed: D10.2 (A), R10.2
unnamed: D11.1 (K), R11.1
unnamed: D12.1 (K), R12.1
unnamed: D13.1 (K), R13.1
unnamed: D14.1 (K), R14.1
unnamed: D15.1 (K), R15.1
unnamed: D16.1 (K), R16.1
unnamed: D17.1 (K), R17.1
unnamed: D18.1 (K), R18.1
unnamed: R19.1, SW3.16, U8.3 (I1a)
unnamed: R20.1, SW3.15, U8.6 (I1b)
unnamed: R21.1, SW3.14, U8.10 (I1c)
unnamed: R22.1, SW3.13, U8.13 (I1d)
unnamed: R23.1, SW3.12, U7.3 (I1a)
unnamed: R24.1, SW3.11, U7.6 (I1b)
unnamed: R25.1, SW3.10, U7.10 (I1c)
unnamed: R26.1, SW3.9, U7.13 (I1d)
unnamed: R27.1, SW1.16, U3.3 (I1a)
unnamed: R28.1, SW1.15, U3.6 (I1b)
unnamed: R29.1, SW1.14, U3.10 (I1c)
unnamed: R30.1, SW1.13, U3.13 (I1d)
unnamed: R31.1, SW1.12, U4.3 (I1a)
unnamed: R32.1, SW1.11, U4.6 (I1b)
unnamed: R33.1, SW1.10, U4.10 (I1c)
unnamed: R34.1, SW1.9, U4.13 (I1d)
unnamed: U1.3 (Q0), U4.2 (I0a)
unnamed: U1.4 (Q1), U4.5 (I0b)
unnamed: U1.5 (Q2), U4.11 (I0c)
unnamed: U1.6 (Q3), U4.14 (I0d)
unnamed: U2.3 (Q0), U3.2 (I0a)
unnamed: U2.4 (Q1), U3.5 (I0b)
unnamed: U2.5 (Q2), U3.11 (I0c)
unnamed: U2.6 (Q3), U3.14 (I0d)
unnamed: U5.3 (Q0), U7.2 (I0a)
unnamed: U5.4 (Q1), U7.5 (I0b)
unnamed: U5.5 (Q2), U7.11 (I0c)
unnamed: U5.6 (Q3), U7.14 (I0d)
unnamed: U6.3 (Q0), U8.2 (I0a)
unnamed: U6.4 (Q1), U8.5 (I0b)
unnamed: U6.5 (Q2), U8.11 (I0c)
unnamed: U6.6 (Q3), U8.14 (I0d)
PROG: D10.1 (K), SW2.3 (C), U3.1 (S), U4.1 (S), U7.1 (S), U8.1 (S)
RST: U1.15 (Mr), U2.15 (Mr), U5.15 (Mr), U6.15 (Mr)
|MAR_IN_16: U1.9 (E1), U1.10 (E2), U2.9 (E1), U2.10 (E2), U5.9 (E1), U5.10 (E2), U6.9 (E1), U6.10 (E2)
