Alban098/Breadboard-CPU-Emulator/schematics/Output_Register.kicad_sch

## KiCad design schematics/Output_Register.kicad_sch (2024-12-01)

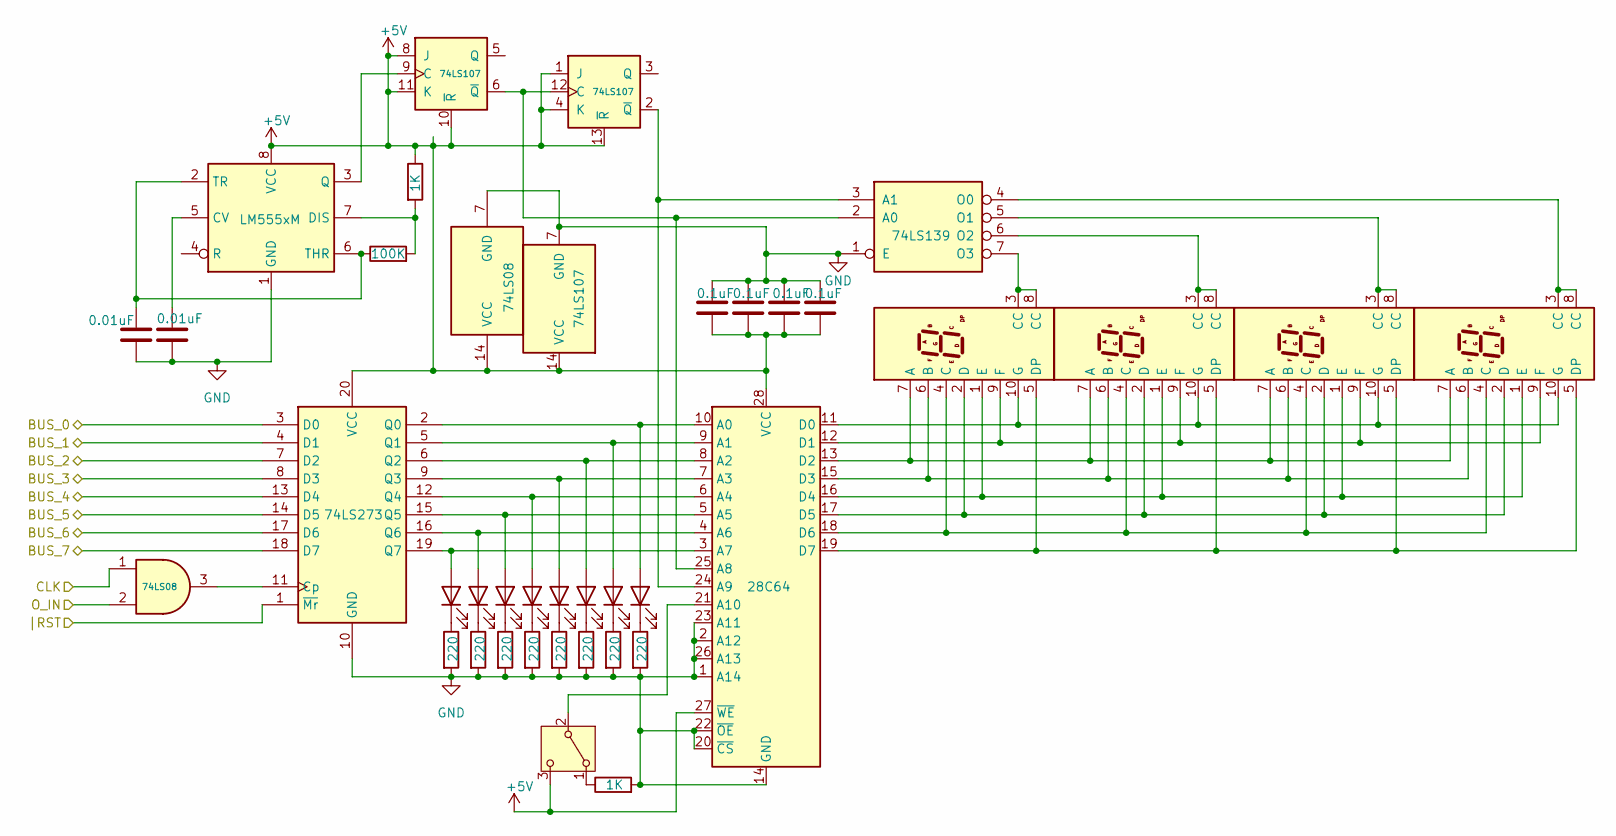
[picture p21: schematic Output_Register.kicad_sch]

Parts:
C1, C2: 0.01uF
C3, C4, C5, C6: 0.1uF
D1, D2, D3, D4, D5, D6, D7, D8: LED
R1, R2, R3, R4, R5, R6, R7, R8: 220
R9, R11: 1K
R10: 100K
SW1: SW_SPDT
U1: 74LS273
U2: 28C64
U3, U4, U5, U6: D168K; D1X8K
U7: 74LS139
U8: 74LS107
U9: LM555xM; SOIC-8_3.9x4.9mm_P1.27mm
U10: 74LS08

Connections:
+5V: C3.2, C4.2, C5.2, C6.2, R9.1, SW1.3 (C), U1.20 (VCC), U2.27 (~WE), U2.28 (VCC), U8.1 (J), U8.4 (K), U8.8 (J), U8.10 (~R), U8.11 (K), U8.13 (~R), U8.14 (VCC), U9.8 (VCC), U10.14 (VCC)
BUS_0: U1.3 (D0)
BUS_1: U1.4 (D1)
BUS_2: U1.7 (D2)
BUS_3: U1.8 (D3)
BUS_4: U1.13 (D4)
BUS_5: U1.14 (D5)
BUS_6: U1.17 (D6)
BUS_7: U1.18 (D7)
CLK: U10.1
GND: C1.2, C2.2, C3.1, C4.1, C5.1, C6.1, R1.2, R2.2, R3.2, R4.2, R5.2, R6.2, R7.2, R8.2, R11.2, U1.10 (GND), U2.1 (A14), U2.2 (A12), U2.14 (GND), U2.20 (~CS), U2.22 (~OE), U2.23 (A11), U2.26 (A13), U7.1 (E), U8.7 (GND), U9.1 (GND), U10.7 (GND)
unnamed: C1.1, R10.1, U9.2 (TR), U9.6 (THR)
unnamed: C2.1, U9.5 (CV)
unnamed: D1.1 (K), R1.1
unnamed: D1.2 (A), U1.19 (Q7), U2.3 (A7)
unnamed: D2.1 (K), R2.1
unnamed: D2.2 (A), U1.16 (Q6), U2.4 (A6)
unnamed: D3.1 (K), R3.1
unnamed: D3.2 (A), U1.15 (Q5), U2.5 (A5)
unnamed: D4.1 (K), R4.1
unnamed: D4.2 (A), U1.12 (Q4), U2.6 (A4)
unnamed: D5.1 (K), R5.1
unnamed: D5.2 (A), U1.9 (Q3), U2.7 (A3)
unnamed: D6.1 (K), R6.1
unnamed: D6.2 (A), U1.6 (Q2), U2.8 (A2)
unnamed: D7.1 (K), R7.1
unnamed: D7.2 (A), U1.5 (Q1), U2.9 (A1)
unnamed: D8.1 (K), R8.1
unnamed: D8.2 (A), U1.2 (Q0), U2.10 (A0)
unnamed: R9.2, R10.2, U9.7 (DIS)
unnamed: R11.1, SW1.1 (A)
unnamed: SW1.2 (B), U2.21 (A10)
unnamed: U1.11 (Cp), U10.3
unnamed: U2.11 (D0), U3.10 (G), U4.10 (G), U5.10 (G), U6.10 (G)
unnamed: U2.12 (D1), U3.9 (F), U4.9 (F), U5.9 (F), U6.9 (F)
unnamed: U2.13 (D2), U3.7 (A), U4.7 (A), U5.7 (A), U6.7 (A)
unnamed: U2.15 (D3), U3.6 (B), U4.6 (B), U5.6 (B), U6.6 (B)
unnamed: U2.16 (D4), U3.1 (E), U4.1 (E), U5.1 (E), U6.1 (E)
unnamed: U2.17 (D5), U3.2 (D), U4.2 (D), U5.2 (D), U6.2 (D)
unnamed: U2.18 (D6), U3.4 (C), U4.4 (C), U5.4 (C), U6.4 (C)
unnamed: U2.19 (D7), U3.5 (DP), U4.5 (DP), U5.5 (DP), U6.5 (DP)
unnamed: U2.24 (A9), U7.3 (A1), U8.2 (~Q)
unnamed: U2.25 (A8), U7.2 (A0), U8.6 (~Q), U8.12 (C)
unnamed: U3.3 (CC), U3.8 (CC), U7.7 (O3)
unnamed: U4.3 (CC), U4.8 (CC), U7.6 (O2)
unnamed: U5.3 (CC), U5.8 (CC), U7.5 (O1)
unnamed: U6.3 (CC), U6.8 (CC), U7.4 (O0)
unnamed: U8.9 (C), U9.3 (Q)
O_IN: U10.2
|RST: U1.1 (~Mr)
