Alban098/Breadboard-CPU-Emulator/schematics/Stack_Pointer.kicad_sch

## KiCad design schematics/Stack_Pointer.kicad_sch (2024-12-01)

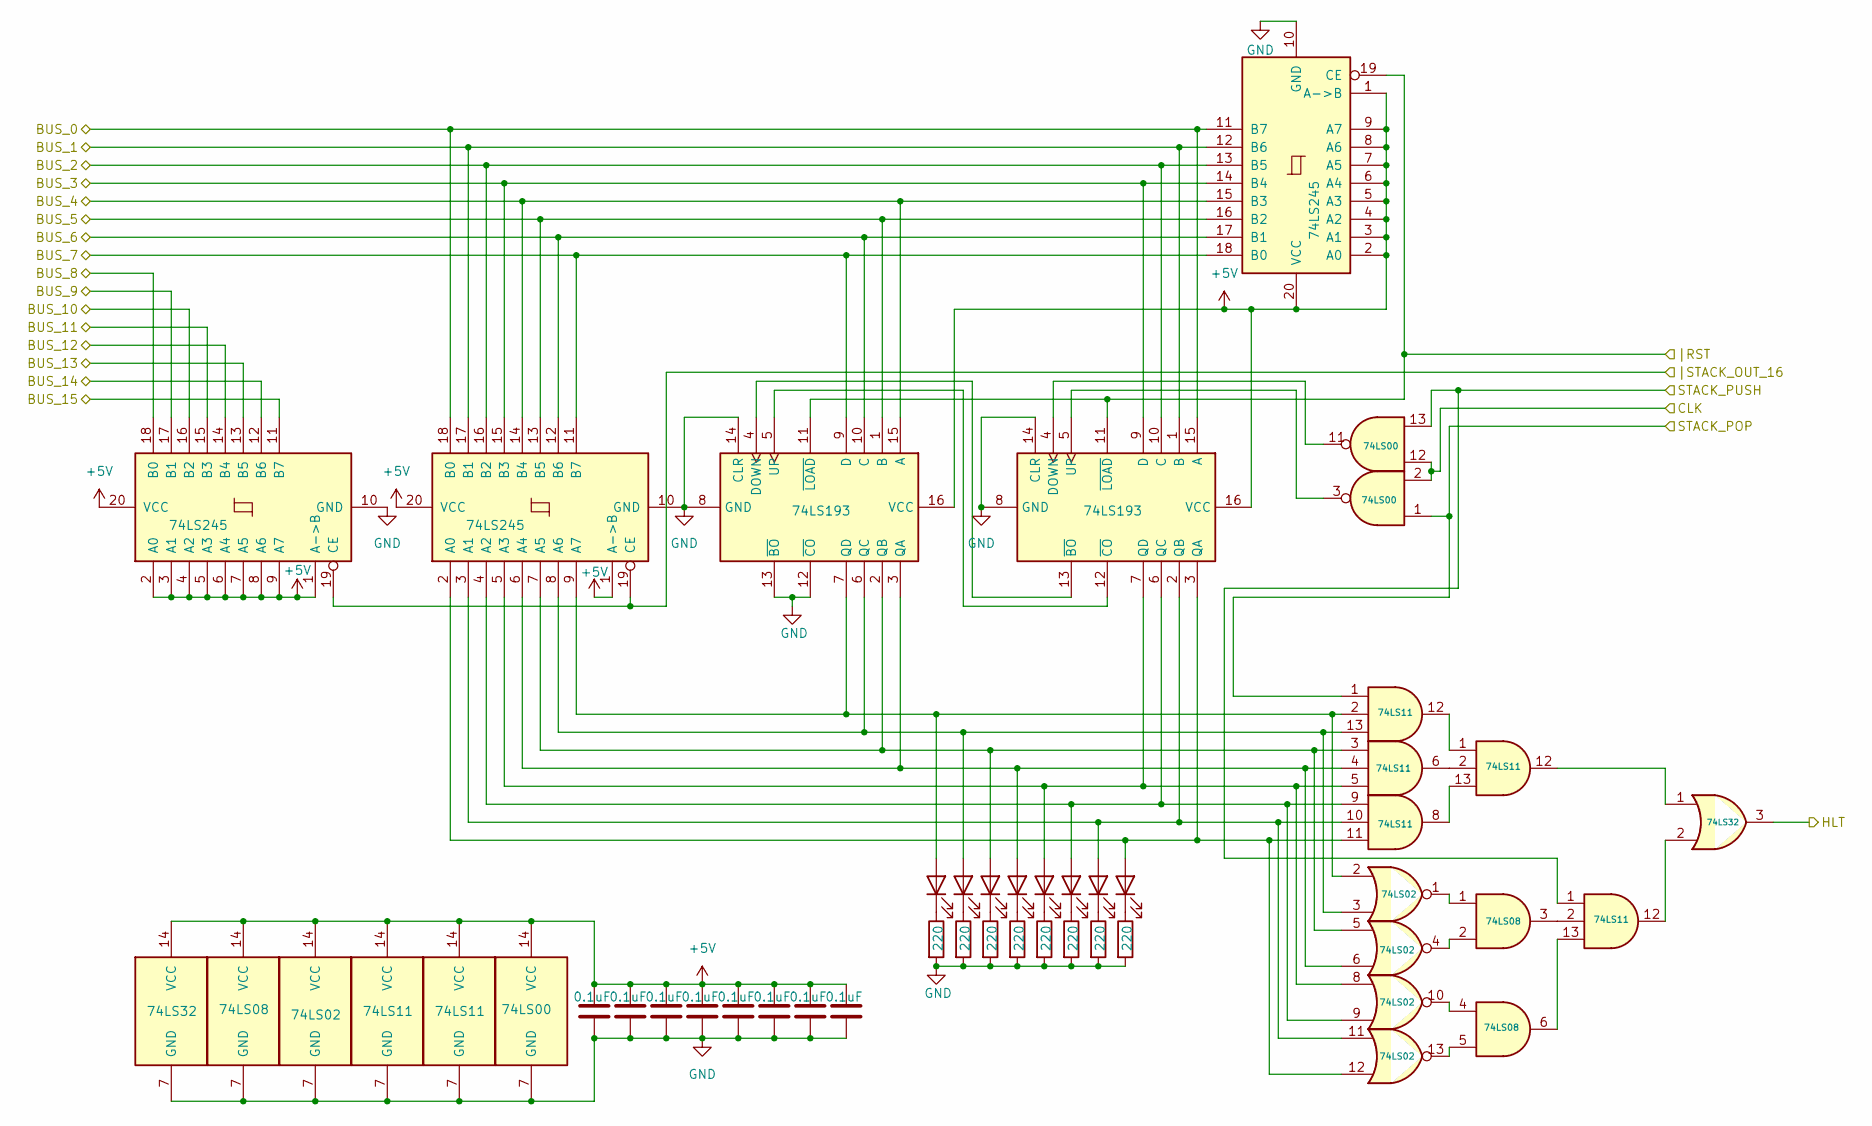
[picture p22: schematic Stack_Pointer.kicad_sch]

Parts:
C1, C2, C3, C4, C5, C6, C7, C8: 0.1uF
D9, D10, D11, D12, D13, D14, D15, D16: LED
R9, R10, R11, R12, R13, R14, R15, R16: 220
U1, U4, U9: 74LS11
U2, U3: 74LS00
U5: 74LS02
U6, U7, U8: 74LS245
U10: 74LS08
U11: 74LS32
U15, U16: 74LS193

Connections:
+5V: C1.1, C2.1, C3.1, C4.1, C5.1, C6.1, C7.1, C8.1, U1.14 (VCC), U3.14 (VCC), U4.14 (VCC), U5.14 (VCC), U6.1 (A->B), U6.20 (VCC), U7.1 (A->B), U7.2 (A0), U7.3 (A1), U7.4 (A2), U7.5 (A3), U7.6 (A4), U7.7 (A5), U7.8 (A6), U7.9 (A7), U7.20 (VCC), U8.1 (A->B), U8.2 (A0), U8.3 (A1), U8.4 (A2), U8.5 (A3), U8.6 (A4), U8.7 (A5), U8.8 (A6), U8.9 (A7), U8.20 (VCC), U10.14 (VCC), U11.14 (VCC), U15.16 (VCC), U16.16 (VCC)
BUS_0: U6.18 (B0), U8.11 (B7), U15.15 (A)
BUS_1: U6.17 (B1), U8.12 (B6), U15.1 (B)
BUS_2: U6.16 (B2), U8.13 (B5), U15.10 (C)
BUS_3: U6.15 (B3), U8.14 (B4), U15.9 (D)
BUS_4: U6.14 (B4), U8.15 (B3), U16.15 (A)
BUS_5: U6.13 (B5), U8.16 (B2), U16.1 (B)
BUS_6: U6.12 (B6), U8.17 (B1), U16.10 (C)
BUS_7: U6.11 (B7), U8.18 (B0), U16.9 (D)
BUS_8: U7.18 (B0)
BUS_9: U7.17 (B1)
BUS_10: U7.16 (B2)
BUS_11: U7.15 (B3)
BUS_12: U7.14 (B4)
BUS_13: U7.13 (B5)
BUS_14: U7.12 (B6)
BUS_15: U7.11 (B7)
CLK: U2.2, U2.12
GND: C1.2, C2.2, C3.2, C4.2, C5.2, C6.2, C7.2, C8.2, R9.2, R10.2, R11.2, R12.2, R13.2, R14.2, R15.2, R16.2, U1.7 (GND), U3.7 (GND), U4.7 (GND), U5.7 (GND), U6.10 (GND), U7.10 (GND), U8.10 (GND), U10.7 (GND), U11.7 (GND), U15.8 (GND), U15.14 (CLR), U16.8 (GND), U16.12 (~CO), U16.13 (~BO), U16.14 (CLR)
HLT: U11.3
unnamed: D9.1 (K), R9.1
unnamed: D9.2 (A), U1.2, U5.2, U6.9 (A7), U16.7 (QD)
unnamed: D10.1 (K), R10.1
unnamed: D10.2 (A), U1.13, U5.3, U6.8 (A6), U16.6 (QC)
unnamed: D11.1 (K), R11.1
unnamed: D11.2 (A), U1.3, U5.5, U6.7 (A5), U16.2 (QB)
unnamed: D12.1 (K), R12.1
unnamed: D12.2 (A), U1.4, U5.6, U6.6 (A4), U16.3 (QA)
unnamed: D13.1 (K), R13.1
unnamed: D13.2 (A), U1.5, U5.8, U6.5 (A3), U15.7 (QD)
unnamed: D14.1 (K), R14.1
unnamed: D14.2 (A), U1.9, U5.9, U6.4 (A2), U15.6 (QC)
unnamed: D15.1 (K), R15.1
unnamed: D15.2 (A), U1.10, U5.11, U6.3 (A1), U15.2 (QB)
unnamed: D16.1 (K), R16.1
unnamed: D16.2 (A), U1.11, U5.12, U6.2 (A0), U15.3 (QA)
unnamed: U1.6, U4.2
unnamed: U1.8, U4.13
unnamed: U1.12, U4.1
unnamed: U5.1, U10.1
unnamed: U5.4, U10.2
unnamed: U9.2, U10.3
unnamed: U5.10, U10.4
unnamed: U5.13, U10.5
unnamed: U9.13, U10.6
unnamed: U4.12, U11.1
unnamed: U9.12, U11.2
unnamed: U2.11, U15.4 (DOWN)
unnamed: U2.3, U15.5 (UP)
unnamed: U15.12 (~CO), U16.5 (UP)
unnamed: U15.13 (~BO), U16.4 (DOWN)
STACK_POP: U1.1, U2.1
STACK_PUSH: U2.13, U9.1
|RST: U8.19 (CE), U15.11 (~LOAD), U16.11 (~LOAD)
|STACK_OUT_16: U6.19 (CE), U7.19 (CE)
