Alban098/Breadboard-CPU-Emulator/schematics/Status_Register.kicad_sch

## KiCad design schematics/Status_Register.kicad_sch (2024-12-01)

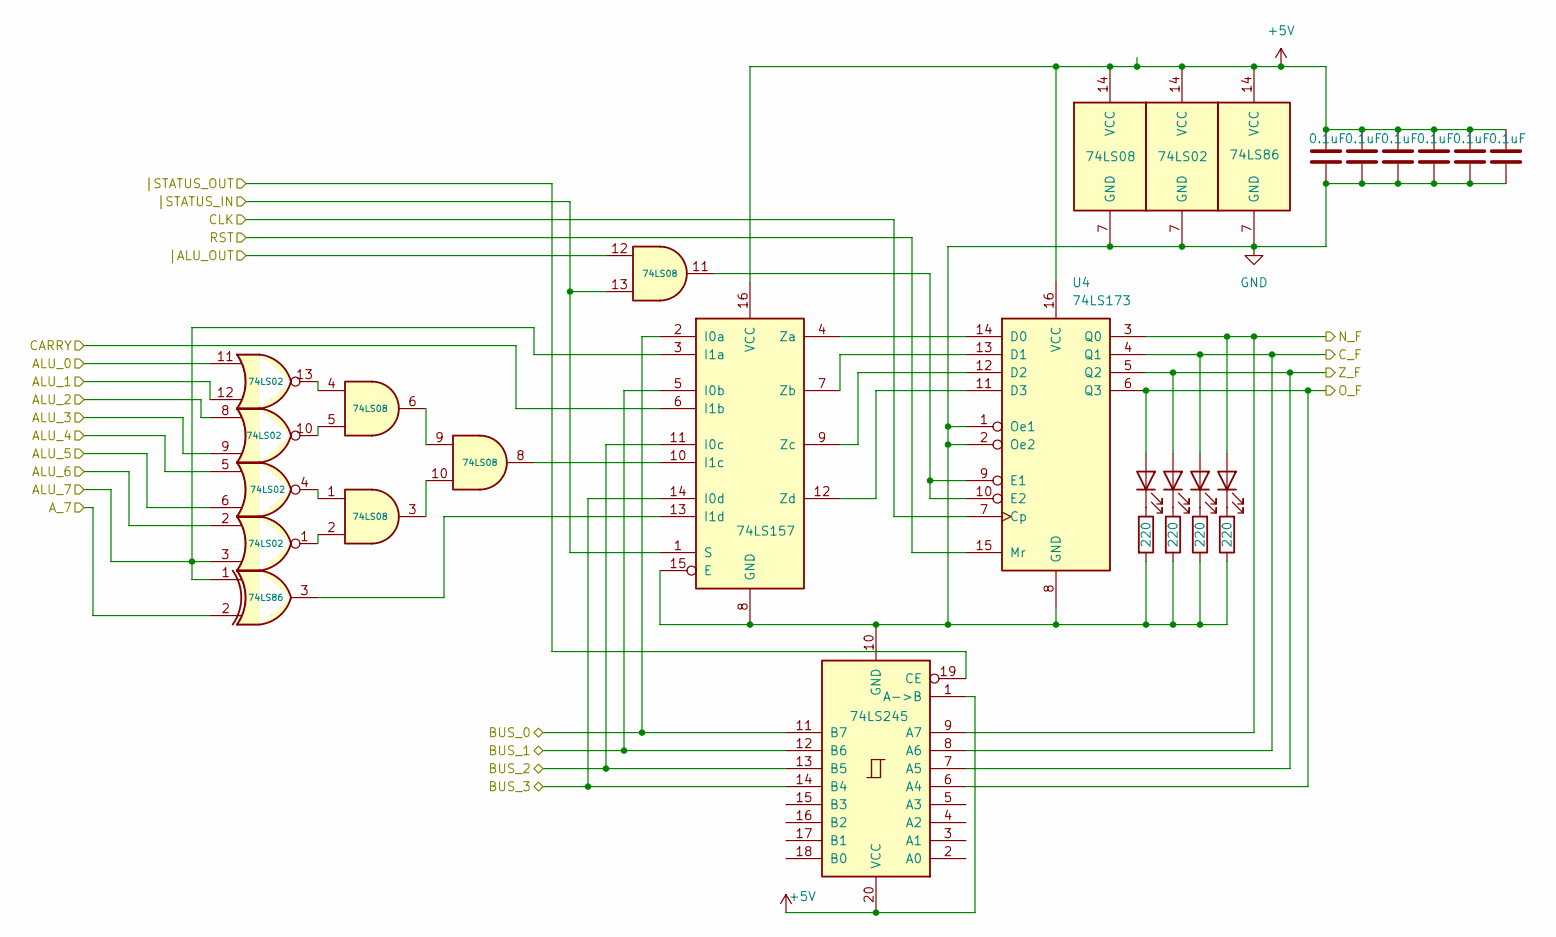
[picture p23: schematic Status_Register.kicad_sch]

Parts:
C1, C2, C3, C4, C5, C6: 0.1uF
D1, D2, D3, D4: LED
R1, R2, R3, R4: 220
U1: 74LS02
U2: 74LS08
U3: 74LS86
U4: 74LS173
U5: 74LS157
U6: 74LS245

Connections:
+5V: C1.1, C2.1, C3.1, C4.1, C5.1, C6.1, U1.14 (VCC), U2.14 (VCC), U3.14 (VCC), U4.16 (VCC), U5.16 (VCC), U6.1 (A->B), U6.20 (VCC)
ALU_0: U1.11
ALU_1: U1.12
ALU_2: U1.8
ALU_3: U1.9
ALU_4: U1.5
ALU_5: U1.6
ALU_6: U1.2
ALU_7: U1.3, U3.1, U5.3 (I1a)
A_7: U3.2
BUS_0: U5.2 (I0a), U6.11 (B7)
BUS_1: U5.5 (I0b), U6.12 (B6)
BUS_2: U5.11 (I0c), U6.13 (B5)
BUS_3: U5.14 (I0d), U6.14 (B4)
CARRY: U5.6 (I1b)
CLK: U4.7 (Cp)
C_F: D2.2 (A), U4.4 (Q1), U6.8 (A6)
GND: C1.2, C2.2, C3.2, C4.2, C5.2, C6.2, R1.2, R2.1, R3.1, R4.2, U1.7 (GND), U2.7 (GND), U3.7 (GND), U4.1 (Oe1), U4.2 (Oe2), U4.8 (GND), U5.8 (GND), U5.15 (E), U6.10 (GND)
N_F: D3.2 (A), U4.3 (Q0), U6.9 (A7)
unnamed: D1.1 (K), R1.1
unnamed: D2.1 (K), R2.2
unnamed: D3.1 (K), R3.2
unnamed: D4.1 (K), R4.1
unnamed: U1.1, U2.2
unnamed: U1.4, U2.1
unnamed: U1.10, U2.5
unnamed: U1.13, U2.4
unnamed: U2.6, U2.9
unnamed: U2.8, U5.10 (I1c)
unnamed: U2.3, U2.10
unnamed: U2.11, U4.9 (E1), U4.10 (E2)
unnamed: U3.3, U5.13 (I1d)
unnamed: U4.11 (D3), U5.12 (Zd)
unnamed: U4.12 (D2), U5.9 (Zc)
unnamed: U4.13 (D1), U5.7 (Zb)
unnamed: U4.14 (D0), U5.4 (Za)
O_F: D4.2 (A), U4.6 (Q3), U6.6 (A4)
RST: U4.15 (Mr)
Z_F: D1.2 (A), U4.5 (Q2), U6.7 (A5)
|ALU_OUT: U2.12
|STATUS_IN: U2.13, U5.1 (S)
|STATUS_OUT: U6.19 (CE)
